Doroco/ABM/설계파일/final_only/image/colossus-photo3-full.jpg

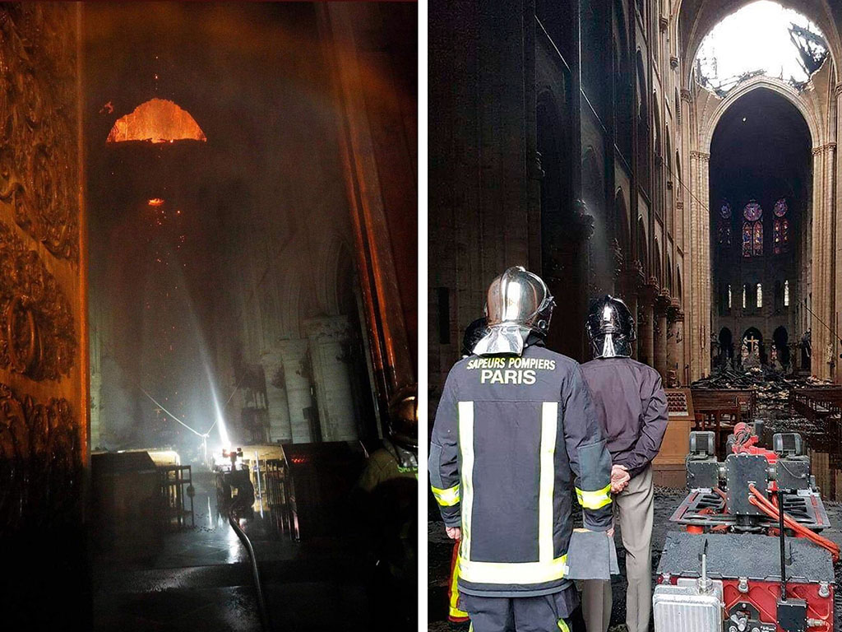
설계파일/final_only/image/colossus-photo3-full.jpg
