Doroco/ABM/설계파일/final_only/image/img/Mobile_bot.jpg

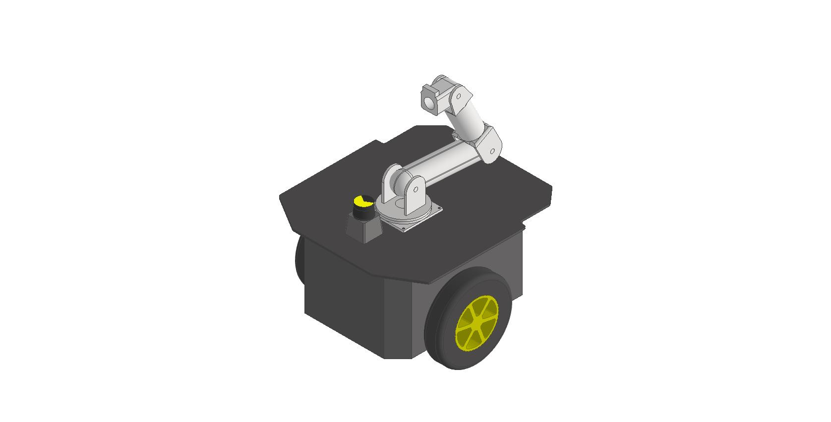
설계파일/final_only/image/img/Mobile_bot.jpg
