Doroco/ABM/설계파일/final_only/image/img/Mobile_bot_2.jpg

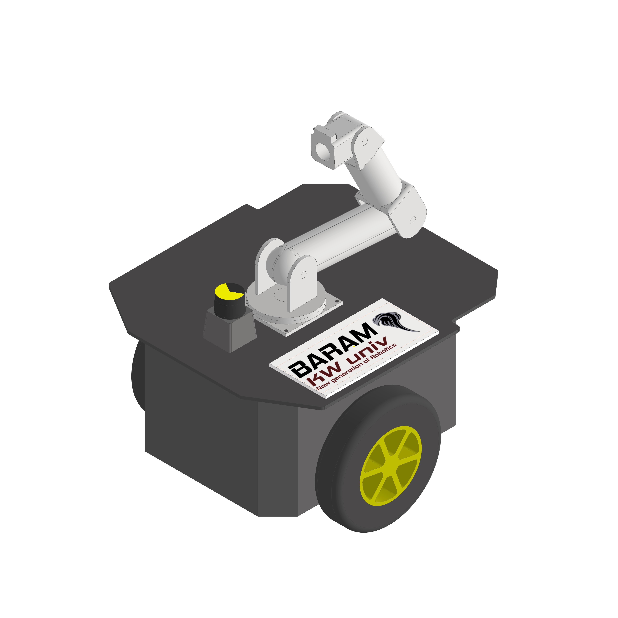
설계파일/final_only/image/img/Mobile_bot_2.jpg
