Doroco/ABM/설계파일/final_only/image/부엉이/1-Figure2-1.png

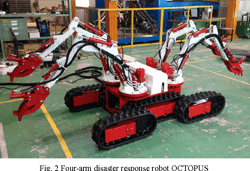
설계파일/final_only/image/부엉이/1-Figure2-1.png
