Doroco/ABM/설계파일/final_only/image/부엉이/재난 로봇.jpg

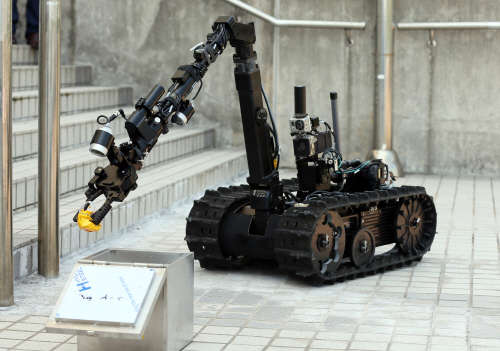
설계파일/final_only/image/부엉이/재난 로봇.jpg
